Ft-Available/RX5808-Div/Img/img0.jpg

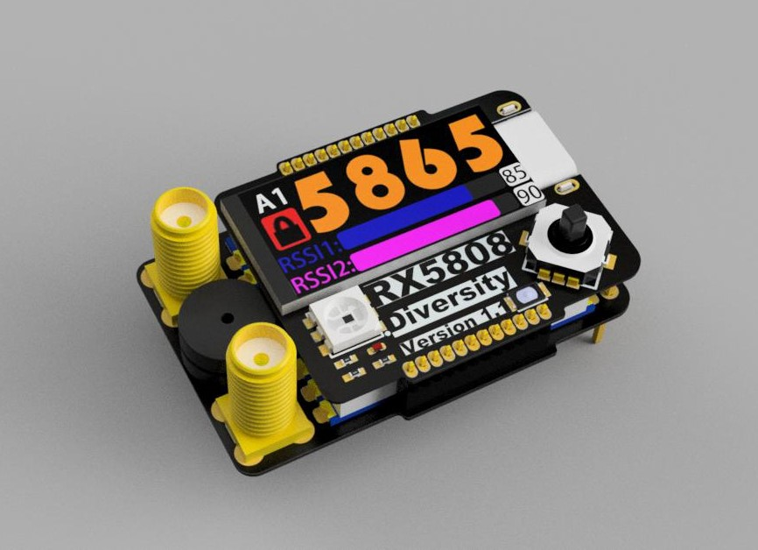
Img/img0.jpg
