Ft-Available/RX5808-Div/Img/img1.png

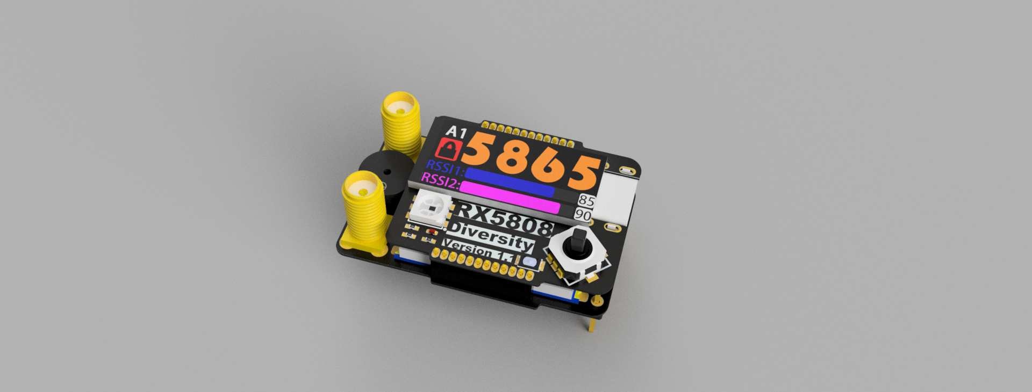
Img/img1.png
