Ft-Available/RX5808-Div/Img/img2.jpg

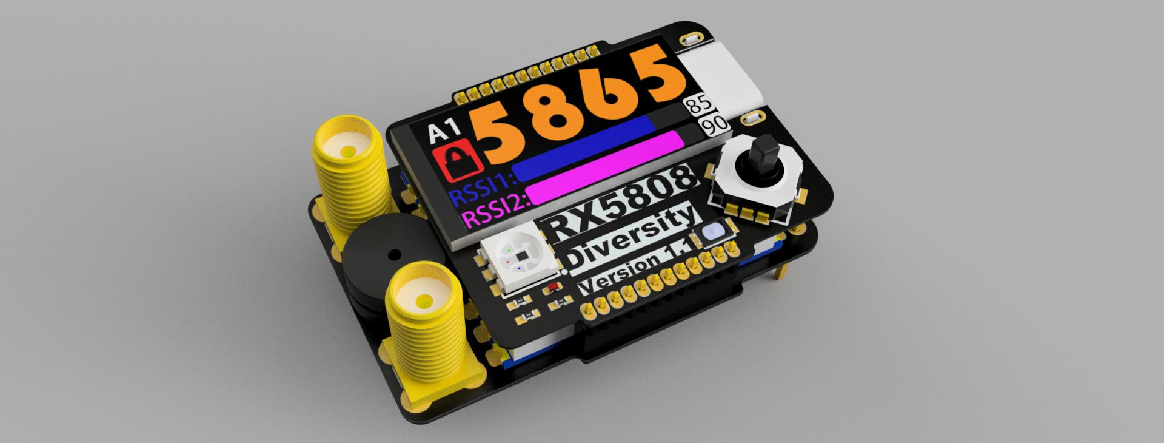
Img/img2.jpg
