Ft-Available/RX5808-Div/Firmware/ESP32/RX5808/main/hardware/lcd.h

#ifndef _LCD_H
#define _LCD_H

#include <stdint.h>


//画笔颜色
#define WHITE         	 0xFFFF
#define BLACK         	 0x0000	  
#define BLUE         	 0x001F  
#define BRED             0XF81F
#define GRED 			 0XFFE0
#define GBLUE			 0X07FF
#define RED           	 0xF800
#define MAGENTA       	 0xF81F
#define GREEN         	 0x07E0
#define CYAN          	 0x7FFF
#define YELLOW        	 0xFFE0
#define BROWN 			 0XBC40 //棕色
#define BRRED 			 0XFC07 //棕红色
#define GRAY  			 0X8430 //灰色
//GUI颜色

#define DARKBLUE      	 0X01CF	//深蓝色
#define LIGHTBLUE      	 0X7D7C	//浅蓝色  
#define GRAYBLUE       	 0X5458 //灰蓝色
//以上三色为PANEL的颜色 
 
#define LIGHTGREEN     	 0X841F //浅绿色
#define LGRAY 			 0XC618 //浅灰色(PANNEL),窗体背景色

#define LGRAYBLUE        0XA651 //浅灰蓝色(中间层颜色)
#define LBBLUE           0X2B12 //浅棕蓝色(选择条目的反色)


			
#define USE_HORIZONTAL 2  //设置横屏或者竖屏显示 0或1为竖屏 2或3为横屏


#if USE_HORIZONTAL==0||USE_HORIZONTAL==1
#define LCD_W 80
#define LCD_H 160

#else
#define LCD_W 160
#define LCD_H 80
#endif


extern uint16_t BACK_COLOR, POINT_COLOR;   

void LCD_GPIO_Init(void);//初始化GPIO
void LCD_Writ_Bus(uint8_t dat);//模拟SPI时序
void LCD_WR_DATA8(uint8_t dat);//写入一个字节
void LCD_WR_DATA(uint16_t dat);//写入两个字节
void LCD_WR_REG(uint8_t dat);//写入一个指令
void Address_Set(uint16_t x1,uint16_t y1,uint16_t x2,uint16_t y2);//设置坐标函数
void LCD_Init(void);//LCD初始化
void LCD_Fill(uint16_t xsta,uint16_t ysta,uint16_t xend,uint16_t yend,uint16_t color);//指定区域填充颜色
void LCD_Clear(void);
void LCD_SET_BLK(int8_t light);
uint16_t LCD_GET_BLK(void);




#endif
