Ft-Available/RX5808-Div/Firmware/ESP32/RX5808/main/hardware/rx5808_config.h

#ifndef __rx5808_config_H
#define __rx5808_config_H


#include <stdint.h>


#define RX5808_CONFIGT_FLASH_EEPROM  0     //0 EEPROM  | 1 FLASH 

#define  STATUS_ON   1
#define  STATUS_OFF  0


#define  START_ANIMATION_DEFAULT  STATUS_ON
#define  BEEP_DEFAULT             STATUS_ON
#define  BACKLIGHT_DEFAULT        100
#define  FAN_SPEED_DEFAULT        100
#define  CHANNEL_DEFAULT          0
#define  RSSI0_MIN_DEFAULT        0
#define  RSSI0_MAX_DEFAULT        4095
#define  RSSI1_MIN_DEFAULT        0
#define  RSSI1_MAX_DEFAULT        4095
#define  OSD_FORMAT_DEFAULT       0
#define  LANGUAGE_DEFAULT         1               //chinese
#define  SIGNAL_SOURCE_DEFAULT    0               //auto

#define  SETUP_ID_DEFAULT         0x1234

	
typedef enum
{
		rx5808_div_config_start_animation=0,
		rx5808_div_config_beep,
		rx5808_div_config_backlight,
		rx5808_div_config_fan_speed,
		rx5808_div_config_channel,
		rx5808_div_config_rssi_adc_value_min0,
		rx5808_div_config_rssi_adc_value_max0,
		rx5808_div_config_rssi_adc_value_min1, 
		rx5808_div_config_rssi_adc_value_max1,
        rx5808_div_config_osd_format,
		rx5808_div_config_language_set,
		rx5808_div_config_signal_source,
		rx5808_div_config_setup_id,
		rx5808_div_config_setup_count,
}rx5808_div_setup_enum;

void rx5808_div_setup_load(void);
void rx5808_div_setup_upload(uint8_t index);
void rx5808_div_setup_upload_start(uint8_t index);


#ifdef __cplusplus
 /*extern "C"*/
#endif




#endif
