Ft-Available/RX5808-Div/Firmware/STM32/HARDWARE/src/system.c

#include "include.h" 
 
void LED_Init()
{
 
  GPIO_InitTypeDef  GPIO_InitStructure;
  RCC_AHB1PeriphClockCmd(RCC_AHB1Periph_GPIOB, ENABLE);

  GPIO_InitStructure.GPIO_Pin = GPIO_Pin_9;
  GPIO_InitStructure.GPIO_Mode = GPIO_Mode_OUT;
  GPIO_InitStructure.GPIO_OType = GPIO_OType_PP;
  GPIO_InitStructure.GPIO_Speed = GPIO_Speed_50MHz;
  GPIO_InitStructure.GPIO_PuPd = GPIO_PuPd_UP;
  GPIO_Init(GPIOB, &GPIO_InitStructure);
  GPIO_ResetBits(GPIOB,GPIO_Pin_9);
	
	
}

void USART_init(u32 bound)
{
  GPIO_InitTypeDef GPIO_InitStructure;
	USART_InitTypeDef USART_InitStructure;
	NVIC_InitTypeDef NVIC_InitStructure;
	RCC_AHB1PeriphClockCmd(RCC_AHB1Periph_GPIOA,ENABLE); 
	RCC_APB2PeriphClockCmd(RCC_APB2Periph_USART1,ENABLE);

	
	GPIO_PinAFConfig(GPIOA,GPIO_PinSource9,GPIO_AF_USART1);
	GPIO_PinAFConfig(GPIOA,GPIO_PinSource10,GPIO_AF_USART1);

	
	GPIO_InitStructure.GPIO_Pin = GPIO_Pin_9 | GPIO_Pin_10; 
	GPIO_InitStructure.GPIO_Mode = GPIO_Mode_AF;
	GPIO_InitStructure.GPIO_Speed = GPIO_Speed_50MHz;	
	GPIO_InitStructure.GPIO_OType = GPIO_OType_PP;
	GPIO_InitStructure.GPIO_PuPd = GPIO_PuPd_UP; 
	GPIO_Init(GPIOA,&GPIO_InitStructure); 


	USART_InitStructure.USART_BaudRate = bound;
	USART_InitStructure.USART_WordLength = USART_WordLength_9b;
	USART_InitStructure.USART_StopBits = USART_StopBits_2;
	USART_InitStructure.USART_Parity = USART_Parity_Even;
	USART_InitStructure.USART_HardwareFlowControl = USART_HardwareFlowControl_None;
	USART_InitStructure.USART_Mode = USART_Mode_Rx;	
	USART_Init(USART1, &USART_InitStructure); 
	USART_Cmd(USART1, ENABLE); 
	USART_ITConfig(USART1, USART_IT_RXNE, ENABLE);

	NVIC_InitStructure.NVIC_IRQChannel = USART1_IRQn;
	NVIC_InitStructure.NVIC_IRQChannelPreemptionPriority=1;
	NVIC_InitStructure.NVIC_IRQChannelSubPriority =1;		
	NVIC_InitStructure.NVIC_IRQChannelCmd = ENABLE;			
	NVIC_Init(&NVIC_InitStructure);	

}

void system_init(void)
{
	NVIC_PriorityGroupConfig(NVIC_PriorityGroup_2);
	SysTick_Delay_Init();
	eeprom_24cxx_init();	
	rx5808_div_setup_load();
	LED_Init();
	LCD_Init();
	Beep_Init();
	//USART_init(115200);  
  RX5808_Init();
	KEY_Init();
	WS2812_init();
	iwdg_init(500);
	//while(1);
	
}
