Ft-Available/RX5808-Div/Firmware/STM32/HARDWARE/inc/key.h

#ifndef __KEY_H
#define __KEY_H

#include "include.h"


#define KEY_UP    PBin(7)
#define KEY_DOWN  PBin(5)
#define KEY_LEFT  PBin(3)
#define KEY_RIGHT PBin(6)
#define KEY_ENTER PBin(4)



void KEY_Init(void);


#endif
