Ft-Available/RX5808-Div/Firmware/ESP32/RX5808/main/gui/lvgl_app/page_start.h

#ifndef __page_start_H
#define __page_start_H



#ifdef __cplusplus
extern "C" {
#endif

    /*********************
    *      INCLUDES
    *********************/
#include "../lvgl/lvgl.h"
    /*********************
    *      DEFINES
    *********************/

    /**********************
    *      TYPEDEFS
    **********************/

    /**********************
    * GLOBAL PROTOTYPES
    **********************/
extern volatile uint8_t start_animation;
void page_start_create(void);
void page_set_animation_en(uint8_t en);
uint16_t page_get_animation_en(void);
    /**********************
    *      MACROS
    **********************/

#ifdef __cplusplus
} /*extern "C"*/
#endif




#endif
