Ft-Available/RX5808-Div/Firmware/ESP32/RX5808/main/gui/lvgl_driver/lv_port_disp.h

/**
 * @file lv_port_disp_templ.h
 *
 */

 /*Copy this file as "lv_port_disp.h" and set this value to "1" to enable content*/
#if 1

#ifndef LV_PORT_DISP_TEMPL_H
#define LV_PORT_DISP_TEMPL_H

#ifdef __cplusplus
extern "C" {
#endif

/*********************
 *      INCLUDES
 *********************/
#include "lvgl/lvgl.h"

/*********************
 *      DEFINES
 *********************/

/**********************
 *      TYPEDEFS
 **********************/

/**********************
 * GLOBAL PROTOTYPES
 **********************/
void lv_port_disp_init(void);
bool get_video_switch(void);
void video_composite_switch(bool flag);
void video_composite_sync_switch(bool flag);
/**********************
 *      MACROS
 **********************/
#ifdef __cplusplus
} /*extern "C"*/
#endif

#endif /*LV_PORT_DISP_TEMPL_H*/

#endif /*Disable/Enable content*/
