Ft-Available/RX5808-Div/Firmware/ESP32/RX5808/main/gui/lvgl_app/page_about.h

#ifndef __page_about_H
#define __page_about_H

 
#ifdef __cplusplus
extern "C" {
#endif

    /*********************
    *      INCLUDES
    *********************/
#include "../lvgl/lvgl.h"
    /*********************
    *      DEFINES
    *********************/

    /**********************
    *      TYPEDEFS
    **********************/

    /**********************
    * GLOBAL PROTOTYPES
    **********************/
    extern lv_indev_t* indev_keypad;


    void page_about_create(void);
		/**********************
    *      MACROS
    **********************/

#ifdef __cplusplus
} /*extern "C"*/
#endif




#endif
