Ft-Available/RX5808-Div/Firmware/ESP32/RX5808/main/gui/lvgl_app/page_scan.h

#ifndef __page_menu_scan_H
#define __page_menu_scan_H



#ifdef __cplusplus
extern "C" {
#endif

    /*********************
    *      INCLUDES
    *********************/
#include "../lvgl/lvgl.h"
    /*********************
    *      DEFINES
    *********************/

    /**********************
    *      TYPEDEFS
    **********************/
    typedef enum
    {
        scan_chart_trigger = 0,
        scan_table_trigger,
    }scan_trigger;
    /**********************
    * GLOBAL PROTOTYPES
    **********************/
    extern lv_indev_t* indev_keypad;
    void page_scan_create(void);
    /**********************
    *      MACROS
    **********************/

#ifdef __cplusplus
} /*extern "C"*/
#endif




#endif
